xoseperez/slices/code/src/config/all.h

#include "version.h"
#include "buildtime.h"
#include "prototypes.h"
#include "general.h"
#include "debug.h"

/*
    If you want to modify the stock configuration but you don't want to touch
    the repo files you can uncomment the following line and add a "custom.h"
    file to this same folder.
*/

//#include "custom.h"
